ddrayne/touch-display-2-mount/docs/p2-full.png

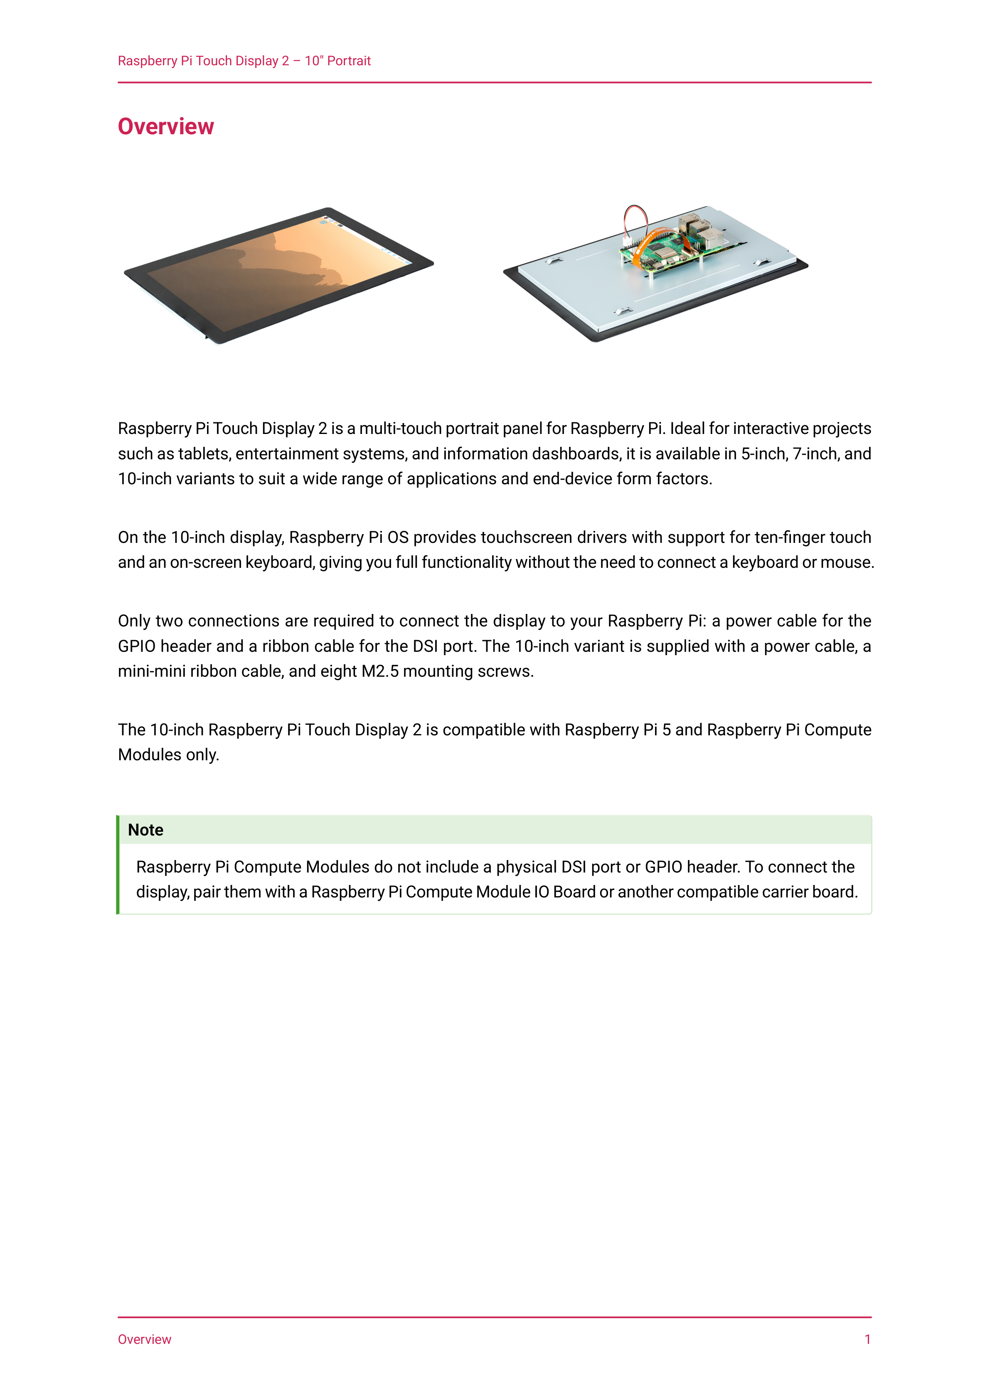
docs/p2-full.png
