ddrayne/touch-display-2-mount/docs/p2-rear-photo.png

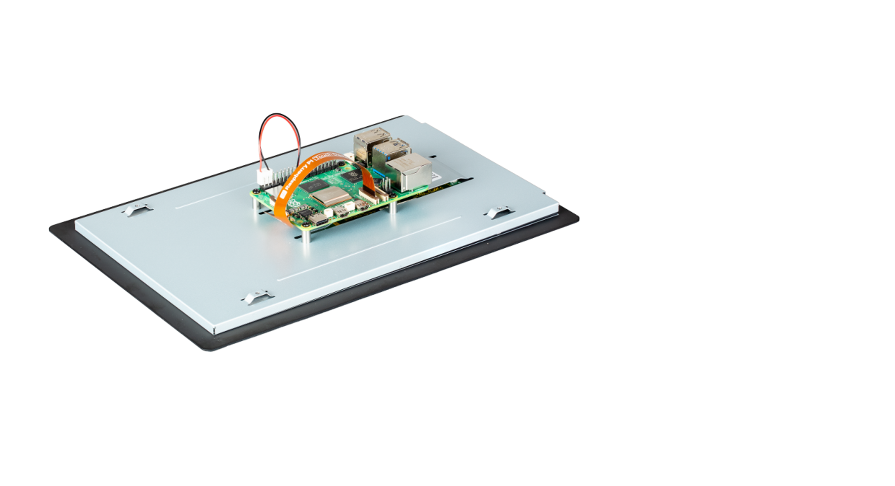
docs/p2-rear-photo.png
