ddrayne/touch-display-2-mount/renders/bezel-back.png

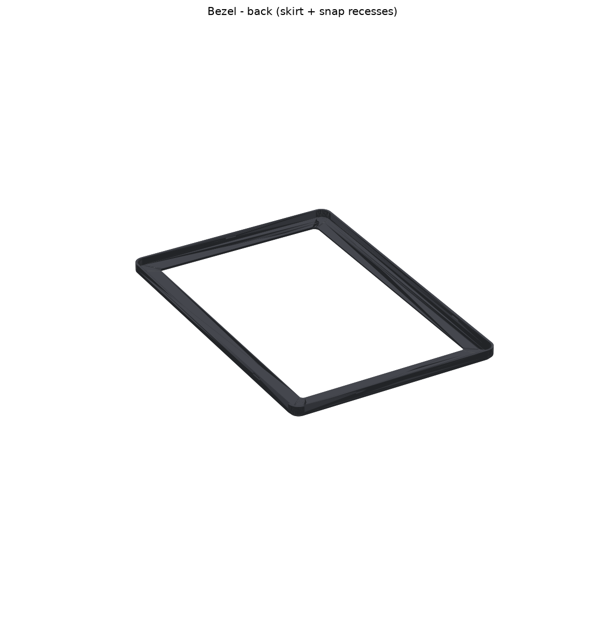
renders/bezel-back.png
