ddrayne/touch-display-2-mount/renders/body-back.png

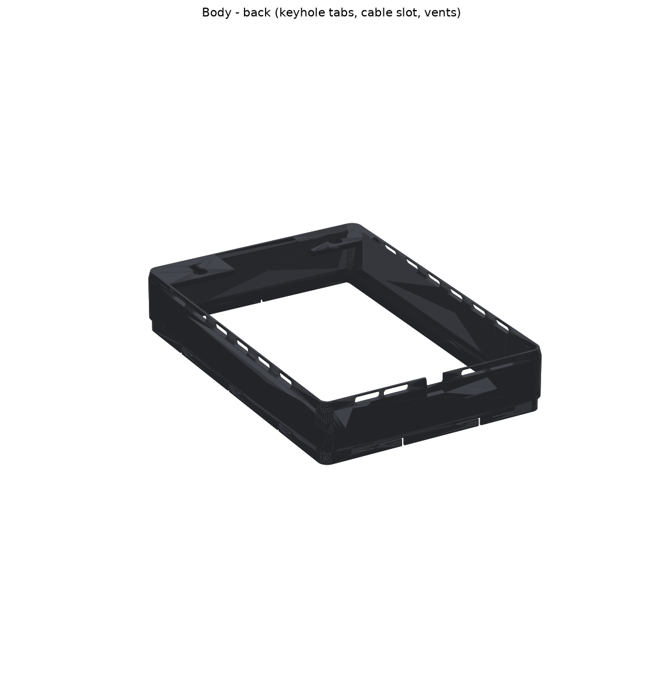
renders/body-back.png
