ddrayne/touch-display-2-mount/renders/body-front.png

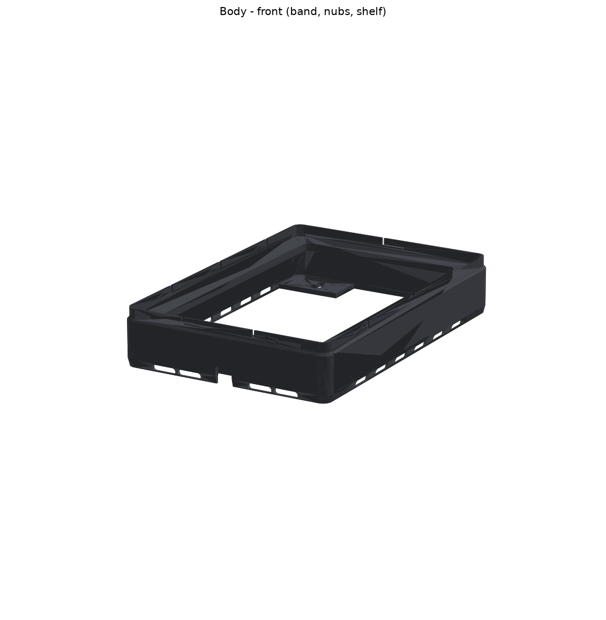
renders/body-front.png
