ddrayne/touch-display-2-mount/renders/cover-back.png

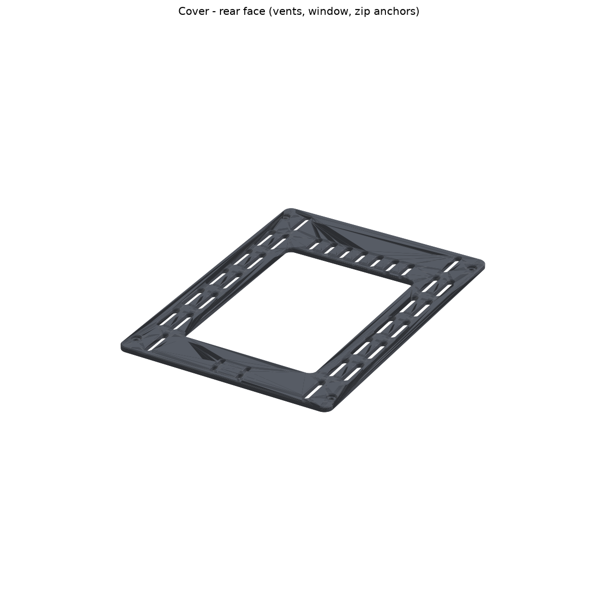
renders/cover-back.png
