ddrayne/touch-display-2-mount/renders/fit-coupon-bezel.png

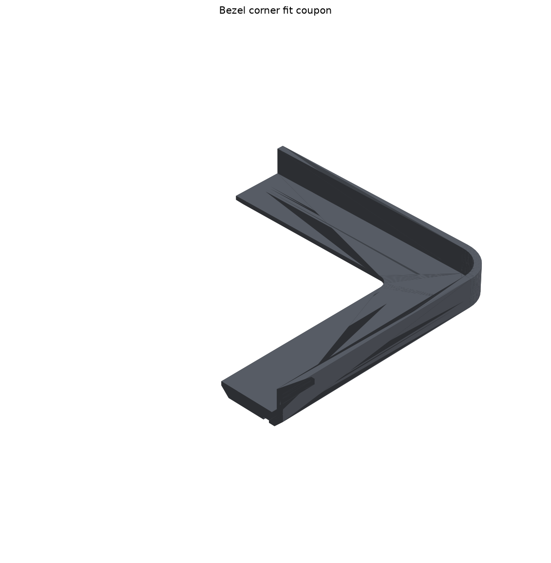
renders/fit-coupon-bezel.png
