ddrayne/touch-display-2-mount/renders/stand-iso.png

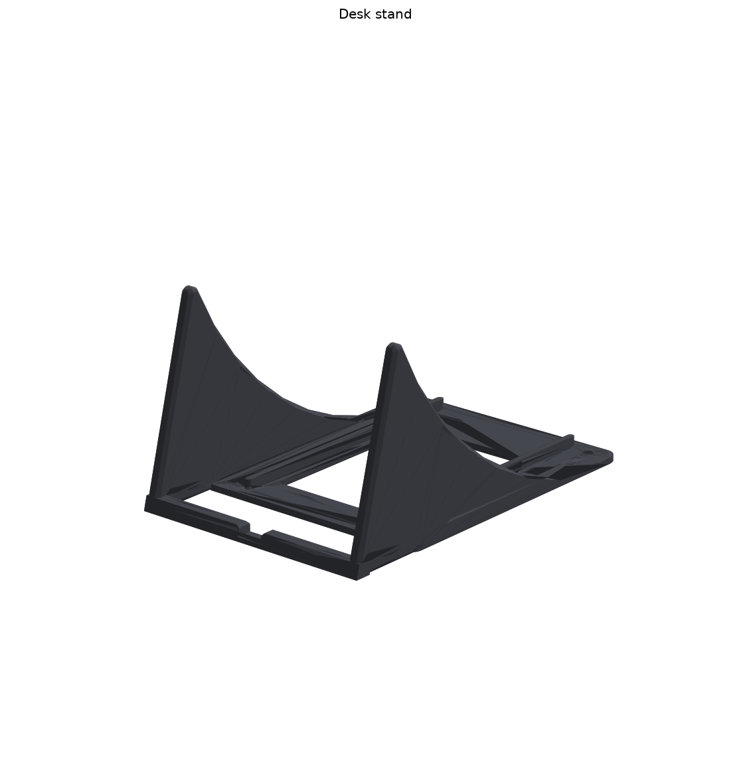
renders/stand-iso.png
