ddrayne/touch-display-2-mount/renders/assembly-chin-pod.png

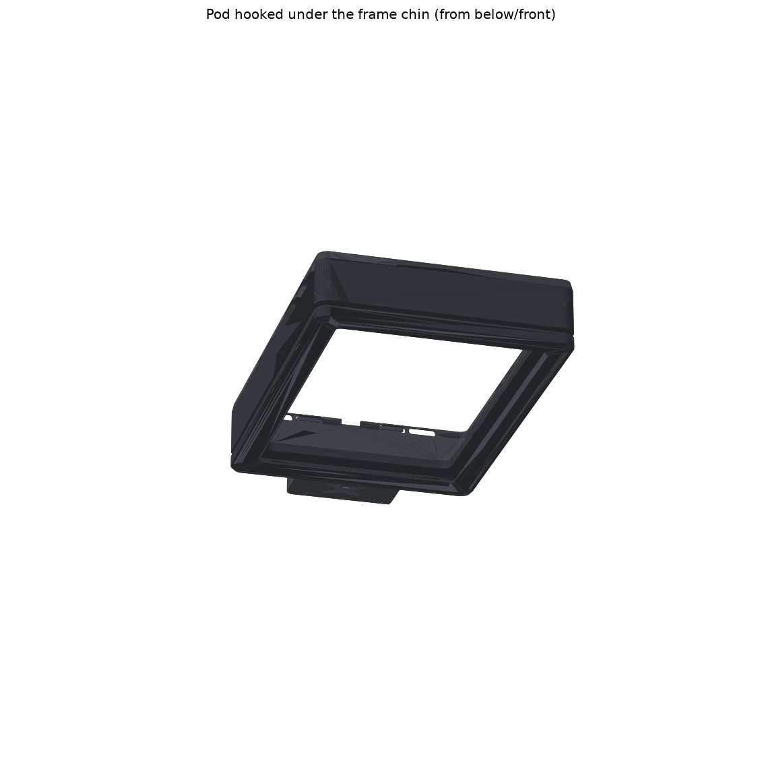
renders/assembly-chin-pod.png
