ddrayne/touch-display-2-mount/renders/assembly-stand-side.png

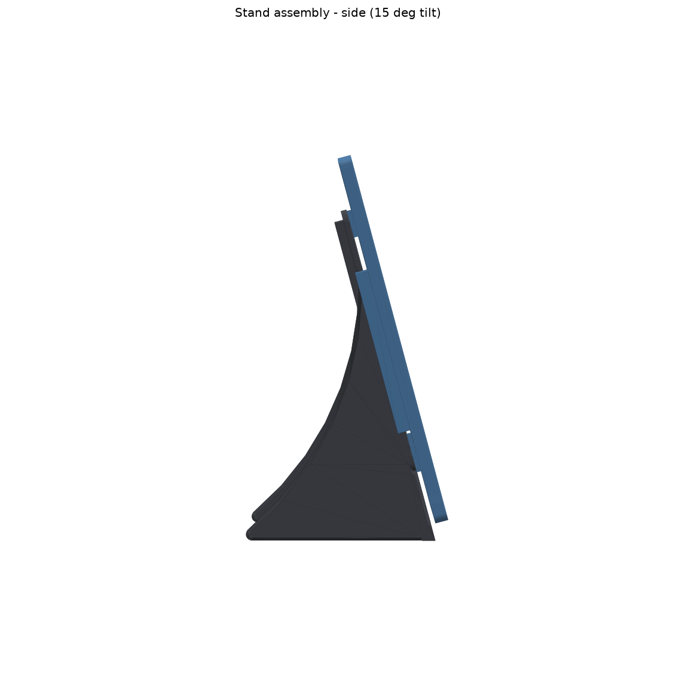
renders/assembly-stand-side.png
