ddrayne/touch-display-2-mount/renders/assembly-stand.png

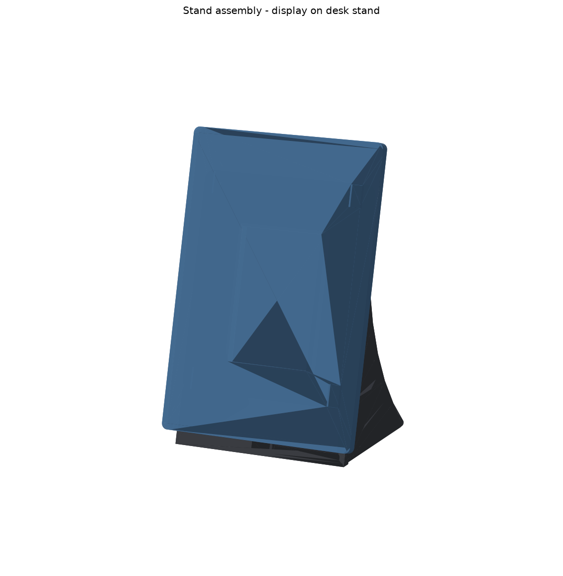
renders/assembly-stand.png
