ddrayne/touch-display-2-mount/renders/assembly-wall-back.png

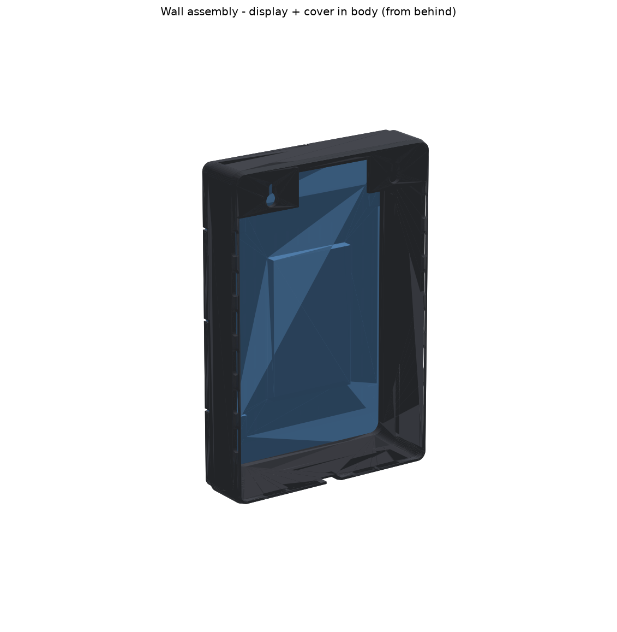
renders/assembly-wall-back.png
